LilRicey12/LED-Heart-Hardware/design/schematics/LED_Hardware_Heart-Final Design.kicad_sch

## KiCad design design/schematics/LED_Hardware_Heart-Final Design.kicad_sch (2026-08-17)

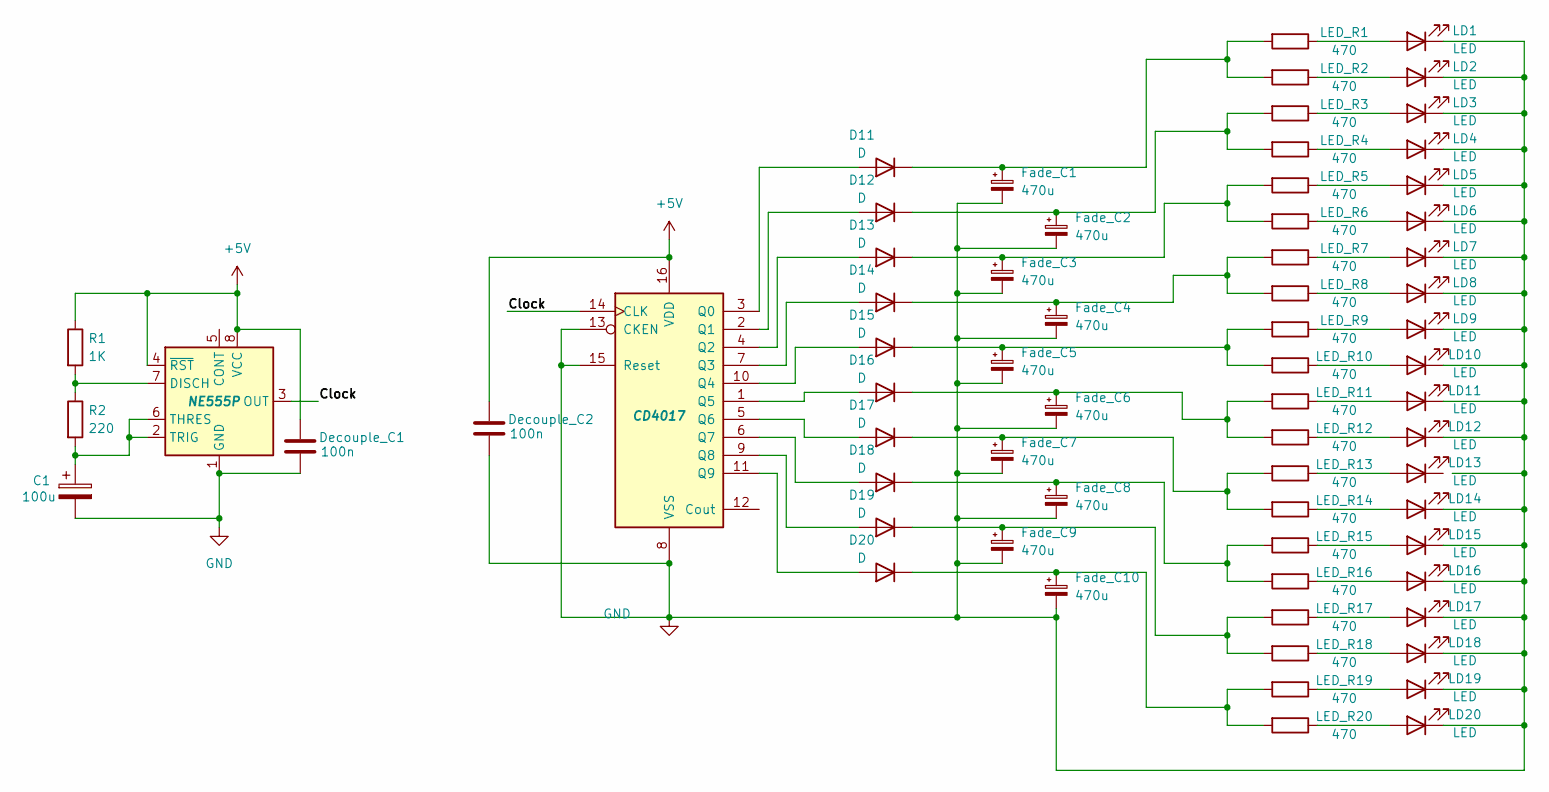
[picture p18: schematic LED_Hardware_Heart-Final Design.kicad_sch]

Parts:
C1: 100u
D11, D12, D13, D14, D15, D16, D17, D18, D19, D20: D
Decouple_C1, Decouple_C2: 100n
Fade_C1, Fade_C2, Fade_C3, Fade_C4, Fade_C5, Fade_C6, Fade_C7, Fade_C8, Fade_C9, Fade_C10: 470u
LD1, LD2, LD3, LD4, LD5, LD6, LD7, LD8, LD9, LD10, LD11, LD12, LD13, LD14, LD15, LD16, LD17, LD18, LD19, LD20: LED
LED_R1, LED_R2, LED_R3, LED_R4, LED_R5, LED_R6, LED_R7, LED_R8, LED_R9, LED_R10, LED_R11, LED_R12, LED_R13, LED_R14, LED_R15, LED_R16, LED_R17, LED_R18, LED_R19, LED_R20: 470
R1: 1K
R2: 220
U1: CD4017
U2: NE555P; DIP-8_W7.62mm

Connections:
+5V: Decouple_C1.1, Decouple_C2.1, R1.1, U1.16 (VDD), U2.4 (~RST), U2.8 (VCC)
Clock: U1.14 (CLK), U2.3 (OUT)
GND: C1.2, Decouple_C1.2, Decouple_C2.2, Fade_C1.2, Fade_C2.2, Fade_C3.2, Fade_C4.2, Fade_C5.2, Fade_C6.2, Fade_C7.2, Fade_C8.2, Fade_C9.2, Fade_C10.2, LD1.1 (K), LD2.1 (K), LD3.1 (K), LD4.1 (K), LD5.1 (K), LD6.1 (K), LD7.1 (K), LD8.1 (K), LD9.1 (K), LD10.1 (K), LD11.1 (K), LD12.1 (K), LD14.1 (K), LD15.1 (K), LD16.1 (K), LD17.1 (K), LD18.1 (K), LD19.1 (K), LD20.1 (K), U1.8 (VSS), U1.13 (CKEN), U1.15 (Reset), U2.1 (GND)
unnamed: C1.1, R2.2, U2.2 (TRIG), U2.6 (THRES)
unnamed: D11.1 (K), Fade_C1.1, LED_R1.2, LED_R2.2
unnamed: D11.2 (A), U1.3 (Q0)
unnamed: D12.1 (K), Fade_C2.1, LED_R3.2, LED_R4.2
unnamed: D12.2 (A), U1.2 (Q1)
unnamed: D13.1 (K), Fade_C3.1, LED_R5.2, LED_R6.2
unnamed: D13.2 (A), U1.4 (Q2)
unnamed: D14.1 (K), Fade_C4.1, LED_R7.2, LED_R8.2
unnamed: D14.2 (A), U1.7 (Q3)
unnamed: D15.1 (K), Fade_C5.1, LED_R9.2, LED_R10.2
unnamed: D15.2 (A), U1.10 (Q4)
unnamed: D16.1 (K), Fade_C6.1, LED_R11.2, LED_R12.2
unnamed: D16.2 (A), U1.1 (Q5)
unnamed: D17.1 (K), Fade_C7.1, LED_R13.2, LED_R14.2
unnamed: D17.2 (A), U1.5 (Q6)
unnamed: D18.1 (K), Fade_C8.1, LED_R15.2, LED_R16.2
unnamed: D18.2 (A), U1.6 (Q7)
unnamed: D19.1 (K), Fade_C9.1, LED_R17.2, LED_R18.2
unnamed: D19.2 (A), U1.9 (Q8)
unnamed: D20.1 (K), Fade_C10.1, LED_R19.2, LED_R20.2
unnamed: D20.2 (A), U1.11 (Q9)
unnamed: LD1.2 (A), LED_R1.1
unnamed: LD2.2 (A), LED_R2.1
unnamed: LD3.2 (A), LED_R3.1
unnamed: LD4.2 (A), LED_R4.1
unnamed: LD5.2 (A), LED_R5.1
unnamed: LD6.2 (A), LED_R6.1
unnamed: LD7.2 (A), LED_R7.1
unnamed: LD8.2 (A), LED_R8.1
unnamed: LD9.2 (A), LED_R9.1
unnamed: LD10.2 (A), LED_R10.1
unnamed: LD11.2 (A), LED_R11.1
unnamed: LD12.2 (A), LED_R12.1
unnamed: LD13.2 (A), LED_R13.1
unnamed: LD14.2 (A), LED_R14.1
unnamed: LD15.2 (A), LED_R15.1
unnamed: LD16.2 (A), LED_R16.1
unnamed: LD17.2 (A), LED_R17.1
unnamed: LD18.2 (A), LED_R18.1
unnamed: LD19.2 (A), LED_R19.1
unnamed: LD20.2 (A), LED_R20.1
unnamed: R1.2, R2.1, U2.7 (DISCH)
