LilRicey12/LED-Heart-Hardware/design/schematics/LED_Hardware_Heart-First_Design.kicad_sch

## KiCad design design/schematics/LED_Hardware_Heart-First_Design.kicad_sch (2026-08-14)

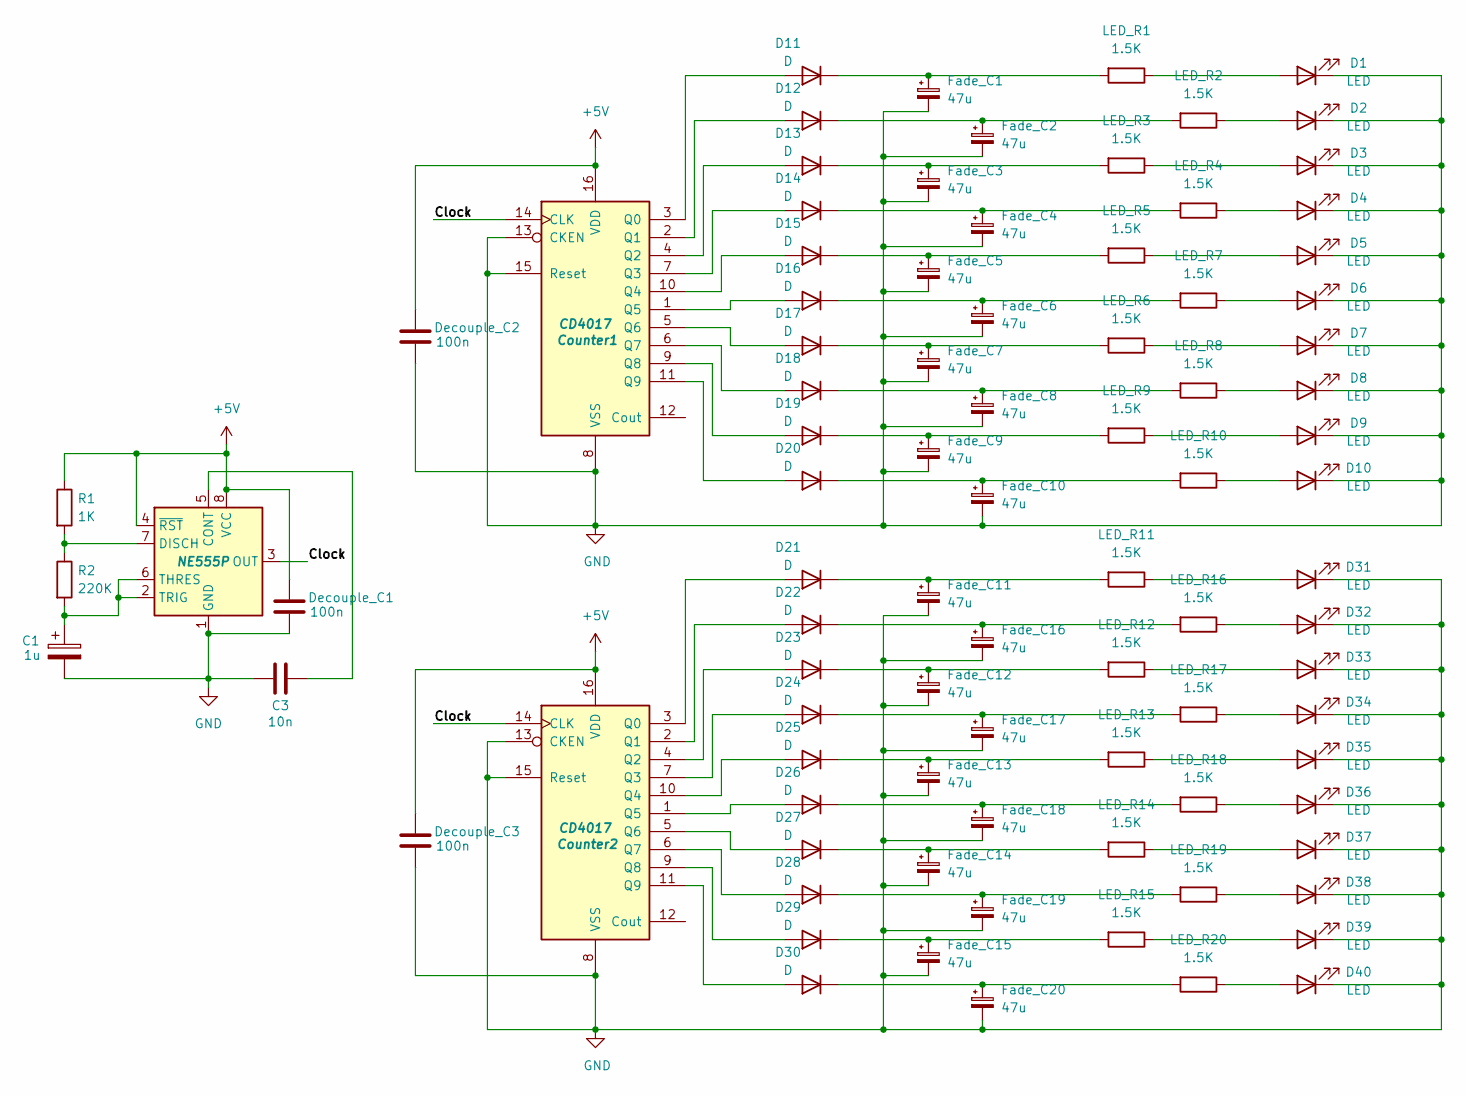
[picture p19: schematic LED_Hardware_Heart-First_Design.kicad_sch]

Parts:
C1: 1u
C3: 10n
Counter1, Counter2: CD4017
D1, D2, D3, D4, D5, D6, D7, D8, D9, D10, D31, D32, D33, D34, D35, D36, D37, D38, D39, D40: LED
D11, D12, D13, D14, D15, D16, D17, D18, D19, D20, D21, D22, D23, D24, D25, D26, D27, D28, D29, D30: D
Decouple_C1, Decouple_C2, Decouple_C3: 100n
Fade_C1, Fade_C2, Fade_C3, Fade_C4, Fade_C5, Fade_C6, Fade_C7, Fade_C8, Fade_C9, Fade_C10, Fade_C11, Fade_C12, Fade_C13, Fade_C14, Fade_C15, Fade_C16, Fade_C17, Fade_C18, Fade_C19, Fade_C20: 47u
LED_R1, LED_R2, LED_R3, LED_R4, LED_R5, LED_R6, LED_R7, LED_R8, LED_R9, LED_R10, LED_R11, LED_R12, LED_R13, LED_R14, LED_R15, LED_R16, LED_R17, LED_R18, LED_R19, LED_R20: 1.5K
R1: 1K
R2: 220K
U3: NE555P; DIP-8_W7.62mm

Connections:
+5V: Counter1.16 (VDD), Counter2.16 (VDD), Decouple_C1.1, Decouple_C2.1, Decouple_C3.1, R1.1, U3.4 (~RST), U3.8 (VCC)
Clock: Counter1.14 (CLK), Counter2.14 (CLK), U3.3 (OUT)
GND: C1.2, C3.2, Counter1.8 (VSS), Counter1.13 (CKEN), Counter1.15 (Reset), Counter2.8 (VSS), Counter2.13 (CKEN), Counter2.15 (Reset), D1.1 (K), D2.1 (K), D3.1 (K), D4.1 (K), D5.1 (K), D6.1 (K), D7.1 (K), D8.1 (K), D9.1 (K), D10.1 (K), D31.1 (K), D32.1 (K), D33.1 (K), D34.1 (K), D35.1 (K), D36.1 (K), D37.1 (K), D38.1 (K), D39.1 (K), D40.1 (K), Decouple_C1.2, Decouple_C2.2, Decouple_C3.2, Fade_C1.2, Fade_C2.2, Fade_C3.2, Fade_C4.2, Fade_C5.2, Fade_C6.2, Fade_C7.2, Fade_C8.2, Fade_C9.2, Fade_C10.2, Fade_C11.2, Fade_C12.2, Fade_C13.2, Fade_C14.2, Fade_C15.2, Fade_C16.2, Fade_C17.2, Fade_C18.2, Fade_C19.2, Fade_C20.2, U3.1 (GND)
unnamed: C1.1, R2.2, U3.2 (TRIG), U3.6 (THRES)
unnamed: C3.1, U3.5 (CONT)
unnamed: Counter1.1 (Q5), D16.2 (A)
unnamed: Counter1.2 (Q1), D12.2 (A)
unnamed: Counter1.3 (Q0), D11.2 (A)
unnamed: Counter1.4 (Q2), D13.2 (A)
unnamed: Counter1.5 (Q6), D17.2 (A)
unnamed: Counter1.6 (Q7), D18.2 (A)
unnamed: Counter1.7 (Q3), D14.2 (A)
unnamed: Counter1.9 (Q8), D19.2 (A)
unnamed: Counter1.10 (Q4), D15.2 (A)
unnamed: Counter1.11 (Q9), D20.2 (A)
unnamed: Counter2.1 (Q5), D26.2 (A)
unnamed: Counter2.2 (Q1), D22.2 (A)
unnamed: Counter2.3 (Q0), D21.2 (A)
unnamed: Counter2.4 (Q2), D23.2 (A)
unnamed: Counter2.5 (Q6), D27.2 (A)
unnamed: Counter2.6 (Q7), D28.2 (A)
unnamed: Counter2.7 (Q3), D24.2 (A)
unnamed: Counter2.9 (Q8), D29.2 (A)
unnamed: Counter2.10 (Q4), D25.2 (A)
unnamed: Counter2.11 (Q9), D30.2 (A)
unnamed: D1.2 (A), LED_R1.1
unnamed: D2.2 (A), LED_R2.1
unnamed: D3.2 (A), LED_R3.1
unnamed: D4.2 (A), LED_R4.1
unnamed: D5.2 (A), LED_R5.1
unnamed: D6.2 (A), LED_R7.1
unnamed: D7.2 (A), LED_R6.1
unnamed: D8.2 (A), LED_R8.1
unnamed: D9.2 (A), LED_R9.1
unnamed: D10.2 (A), LED_R10.1
unnamed: D11.1 (K), Fade_C1.1, LED_R1.2
unnamed: D12.1 (K), Fade_C2.1, LED_R2.2
unnamed: D13.1 (K), Fade_C3.1, LED_R3.2
unnamed: D14.1 (K), Fade_C4.1, LED_R4.2
unnamed: D15.1 (K), Fade_C5.1, LED_R5.2
unnamed: D16.1 (K), Fade_C6.1, LED_R7.2
unnamed: D17.1 (K), Fade_C7.1, LED_R6.2
unnamed: D18.1 (K), Fade_C8.1, LED_R8.2
unnamed: D19.1 (K), Fade_C9.1, LED_R9.2
unnamed: D20.1 (K), Fade_C10.1, LED_R10.2
unnamed: D21.1 (K), Fade_C11.1, LED_R11.2
unnamed: D22.1 (K), Fade_C16.1, LED_R16.2
unnamed: D23.1 (K), Fade_C12.1, LED_R12.2
unnamed: D24.1 (K), Fade_C17.1, LED_R17.2
unnamed: D25.1 (K), Fade_C13.1, LED_R13.2
unnamed: D26.1 (K), Fade_C18.1, LED_R18.2
unnamed: D27.1 (K), Fade_C14.1, LED_R14.2
unnamed: D28.1 (K), Fade_C19.1, LED_R19.2
unnamed: D29.1 (K), Fade_C15.1, LED_R15.2
unnamed: D30.1 (K), Fade_C20.1, LED_R20.2
unnamed: D31.2 (A), LED_R11.1
unnamed: D32.2 (A), LED_R16.1
unnamed: D33.2 (A), LED_R12.1
unnamed: D34.2 (A), LED_R17.1
unnamed: D35.2 (A), LED_R13.1
unnamed: D36.2 (A), LED_R18.1
unnamed: D37.2 (A), LED_R14.1
unnamed: D38.2 (A), LED_R19.1
unnamed: D39.2 (A), LED_R15.1
unnamed: D40.2 (A), LED_R20.1
unnamed: R1.2, R2.1, U3.7 (DISCH)
